dnuke-art/digital-pinhole/mockups/out/curved_grating_sheet.png

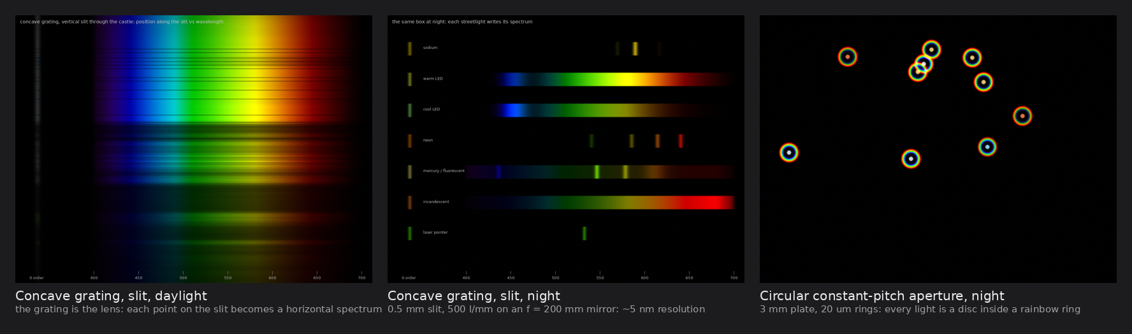
mockups/out/curved_grating_sheet.png
