dnuke-art/digital-pinhole/mockups/out/diag_01_relay.png

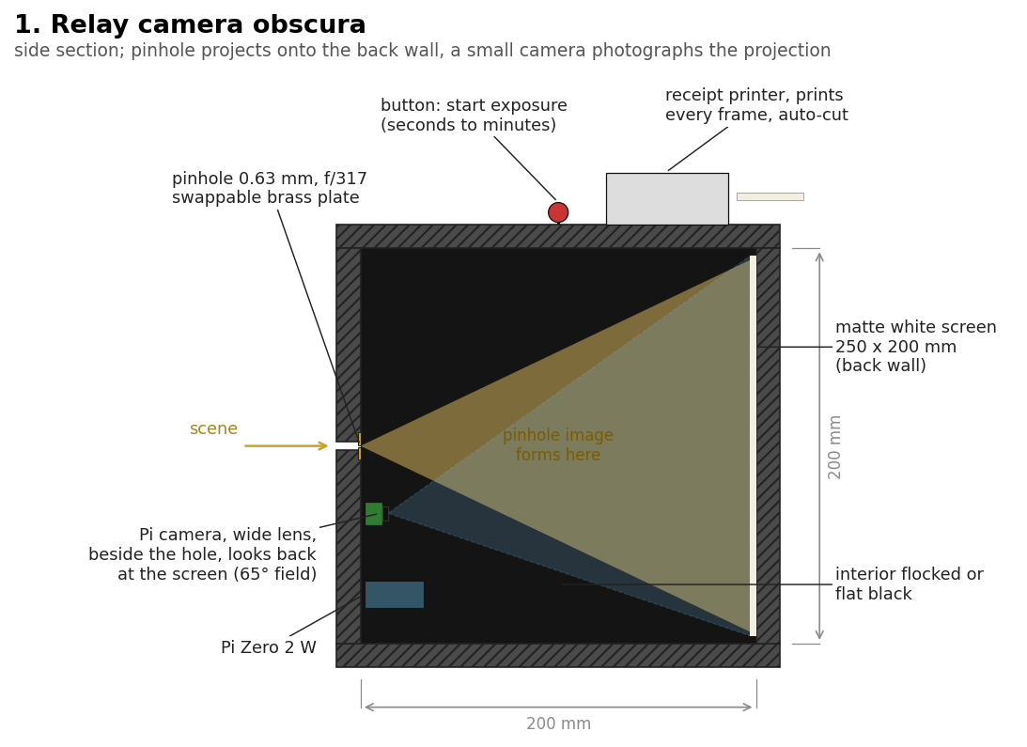
mockups/out/diag_01_relay.png
