dnuke-art/digital-pinhole/mockups/out/diag_02_wetplate.png

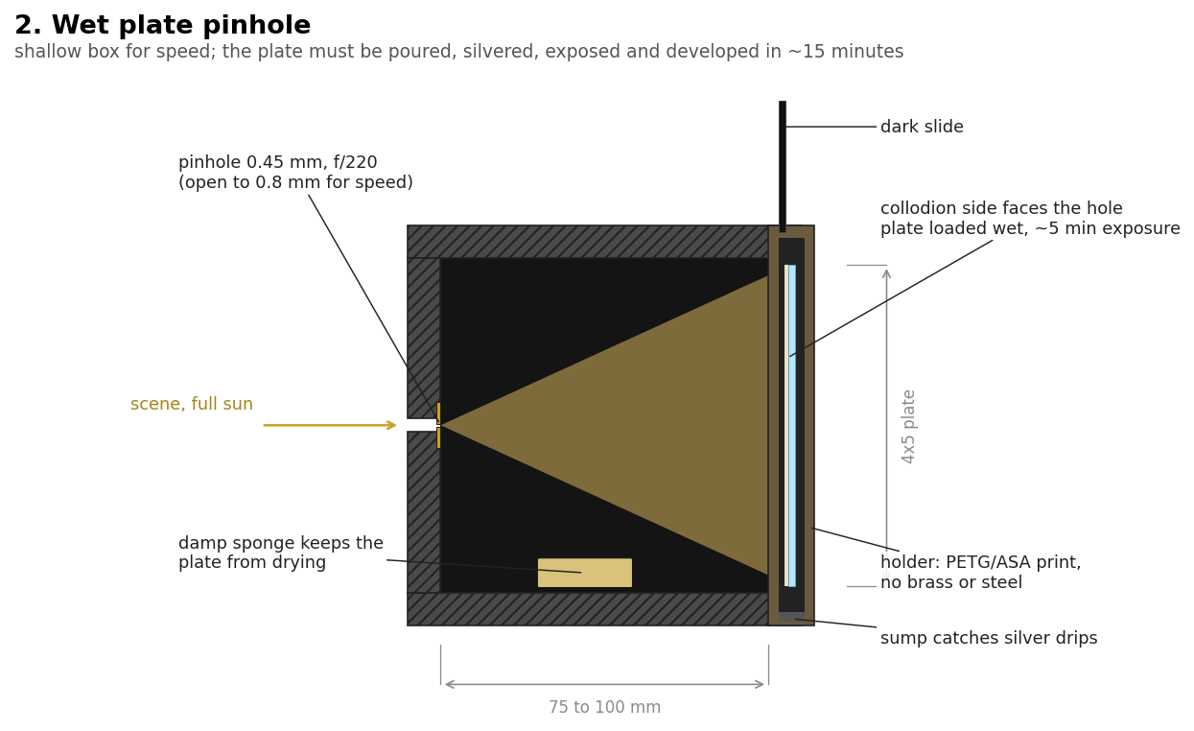
mockups/out/diag_02_wetplate.png
