dnuke-art/digital-pinhole/mockups/out/diag_03_swappable.png

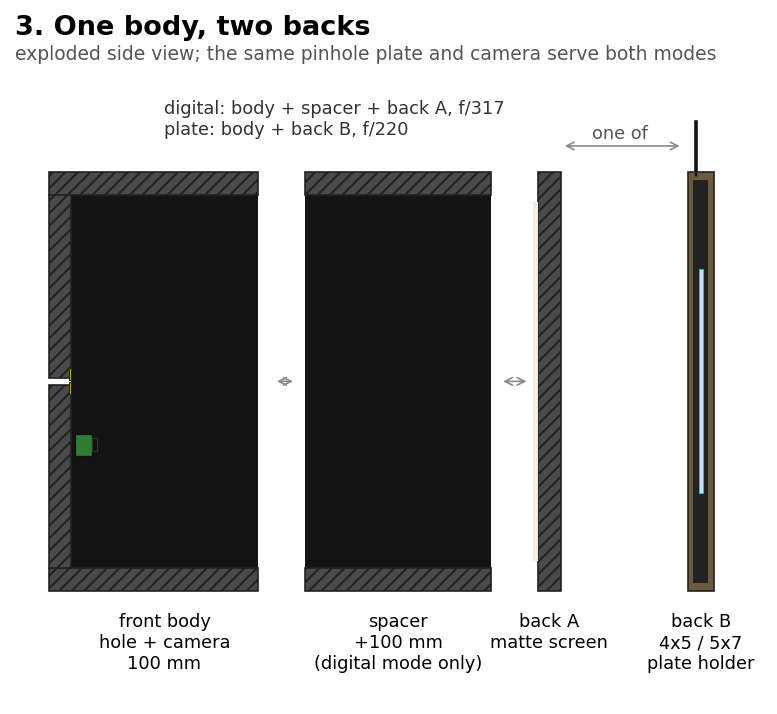
mockups/out/diag_03_swappable.png
