dnuke-art/digital-pinhole/mockups/out/diag_04_pihq.png

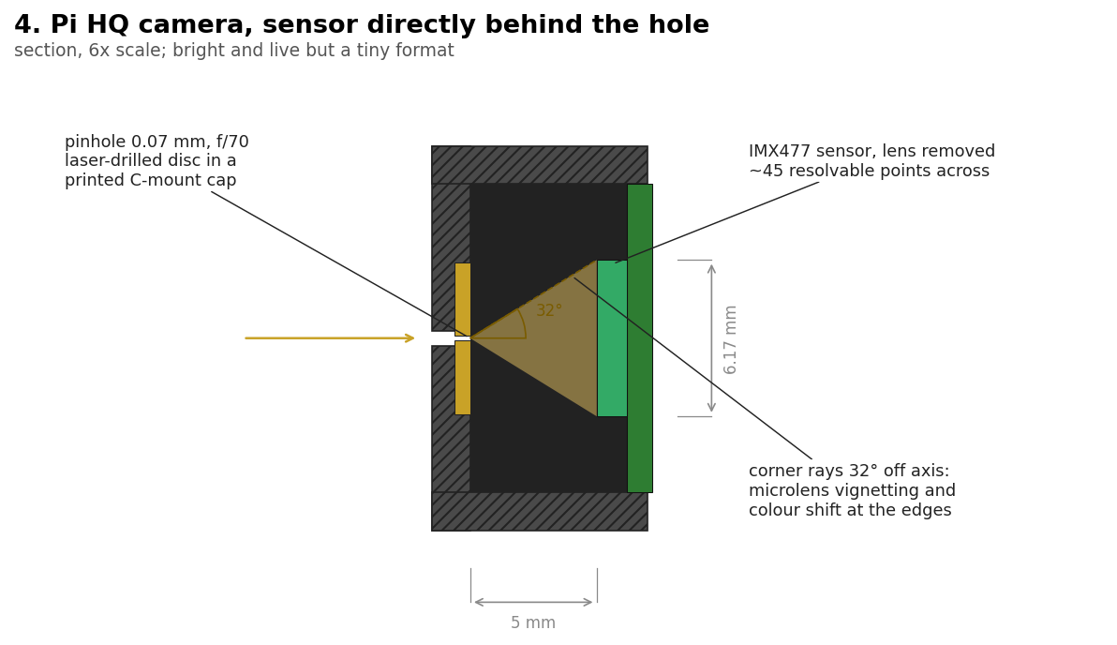
mockups/out/diag_04_pihq.png
