dnuke-art/digital-pinhole/mockups/out/diag_05_bodycap.png

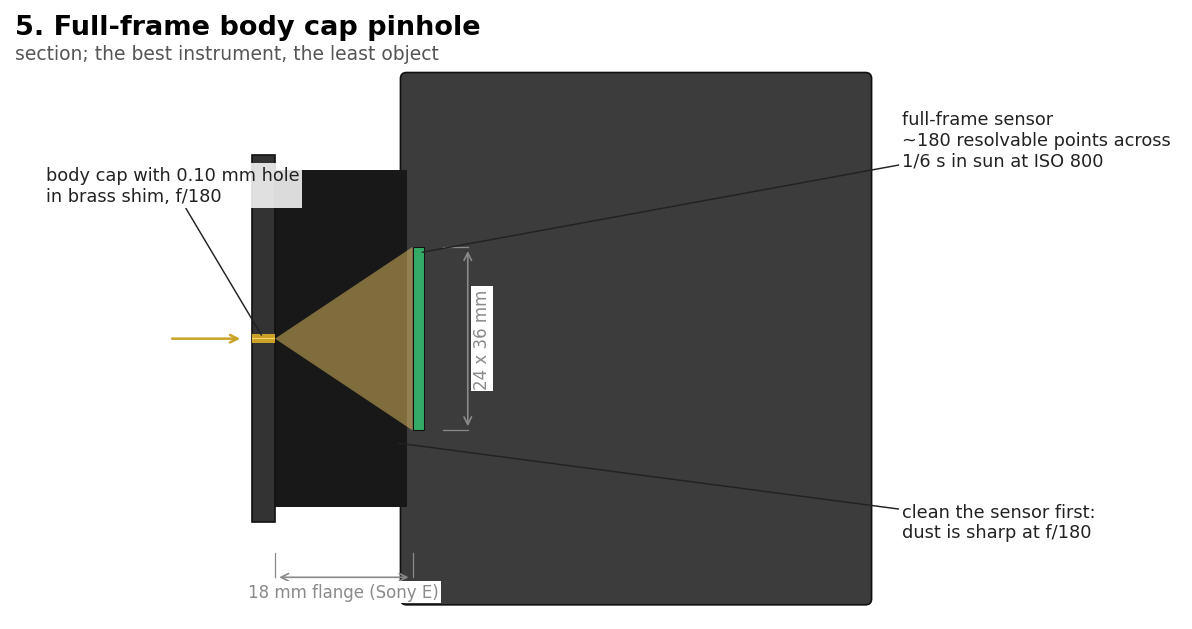
mockups/out/diag_05_bodycap.png
