dnuke-art/digital-pinhole/mockups/out/diag_06_suntrace.png

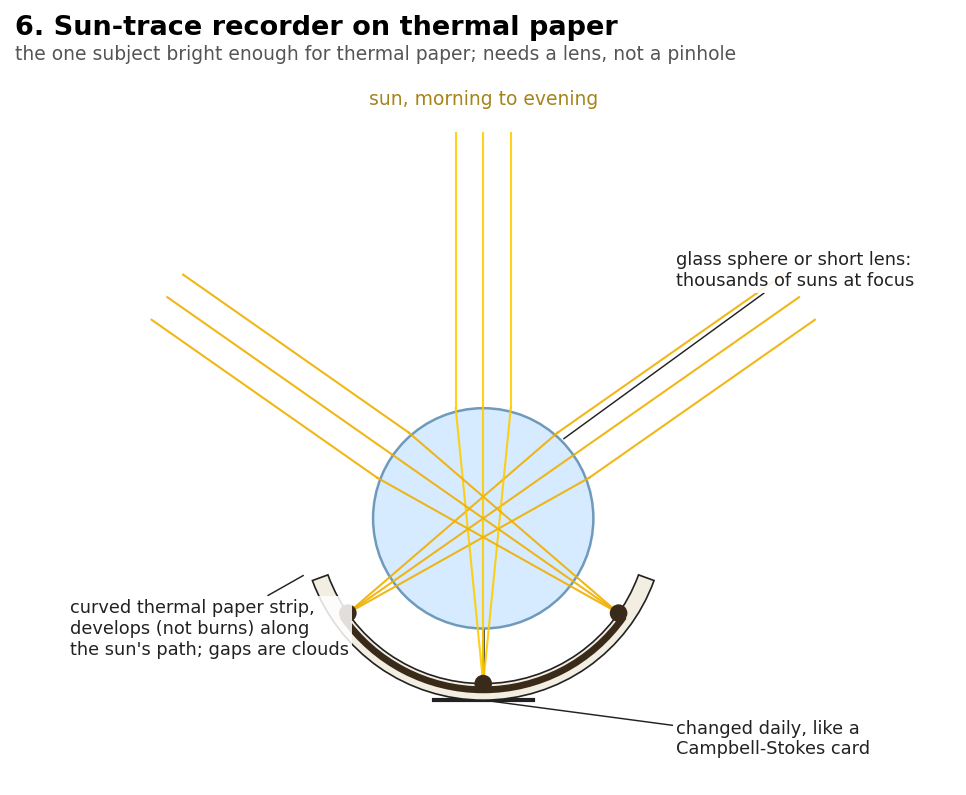
mockups/out/diag_06_suntrace.png
