dnuke-art/digital-pinhole/mockups/out/diag_07_dubroni.png

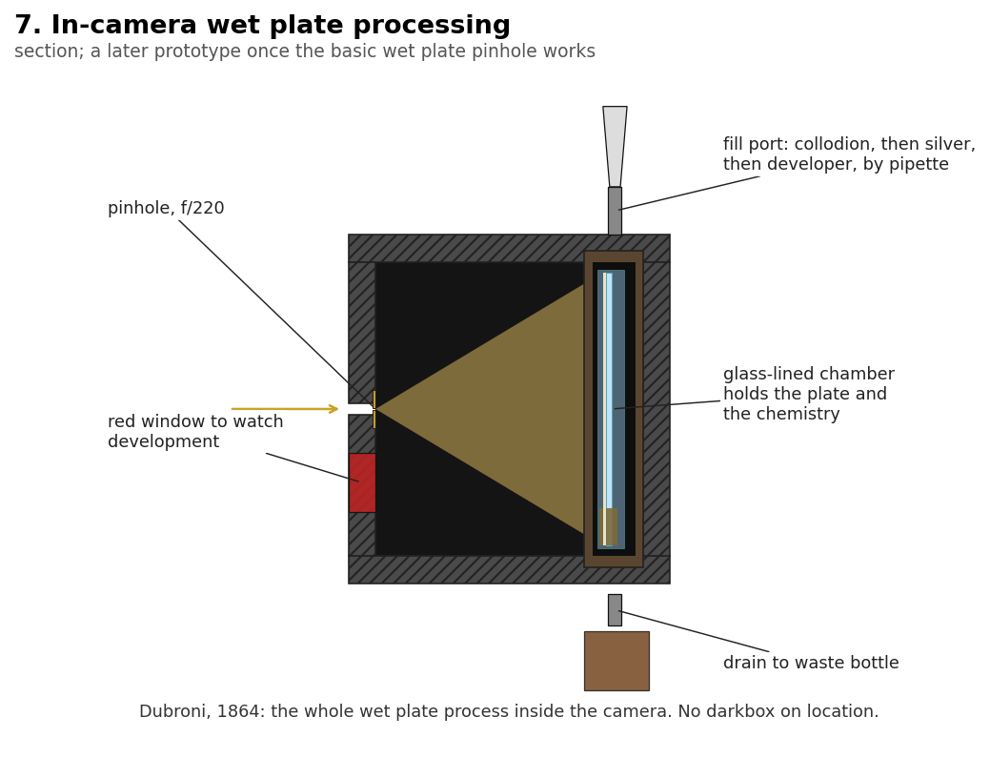
mockups/out/diag_07_dubroni.png
