dnuke-art/digital-pinhole/mockups/out/diag_08_show.png

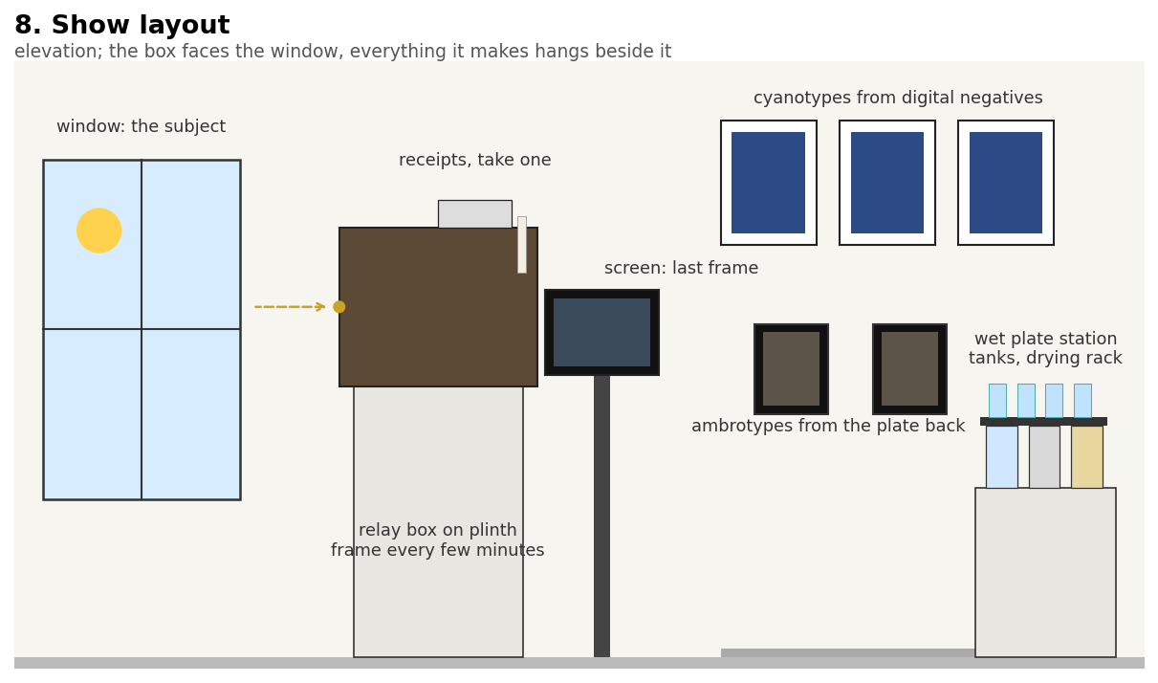
mockups/out/diag_08_show.png
