dnuke-art/digital-pinhole/mockups/out/diag_09_rowland.png

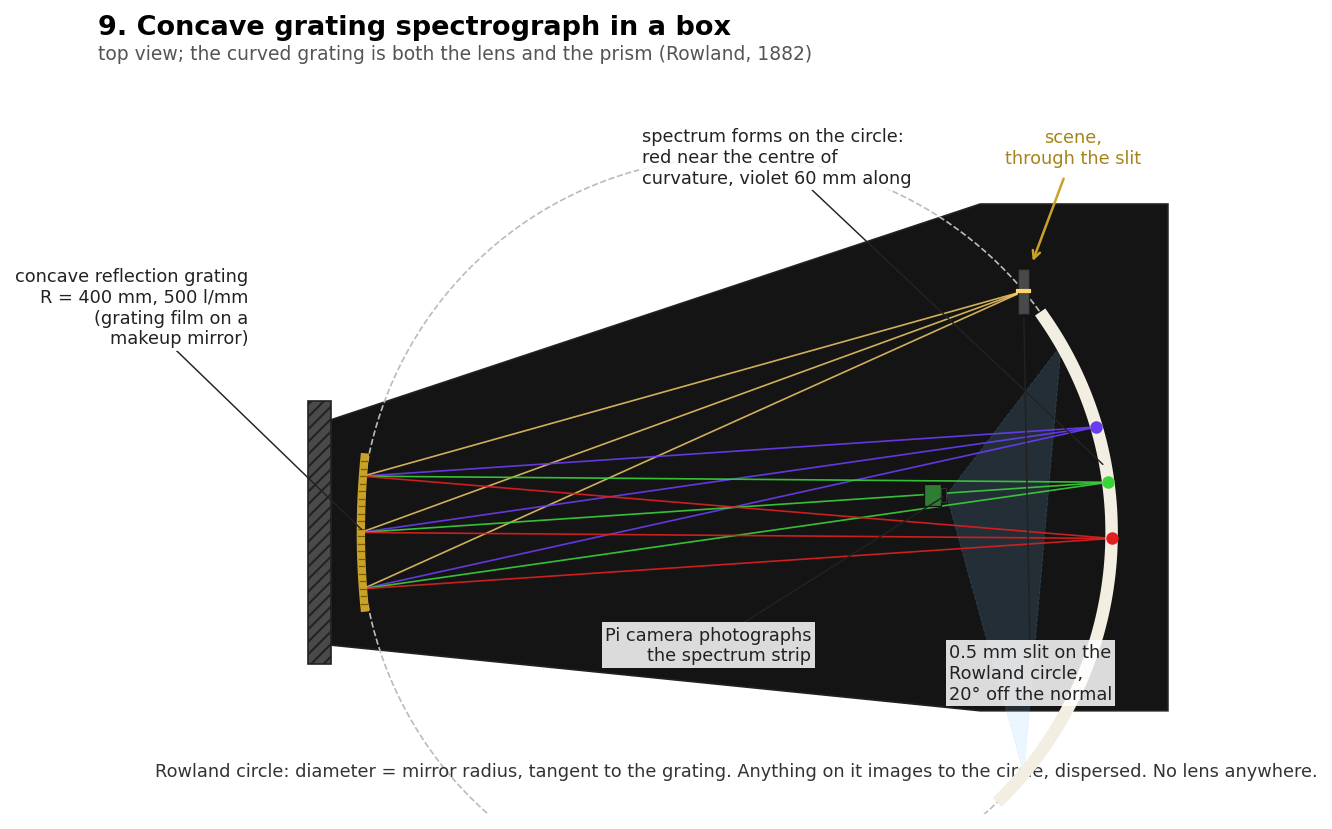
mockups/out/diag_09_rowland.png
