dnuke-art/digital-pinhole/mockups/out/diagrams_sheet.png

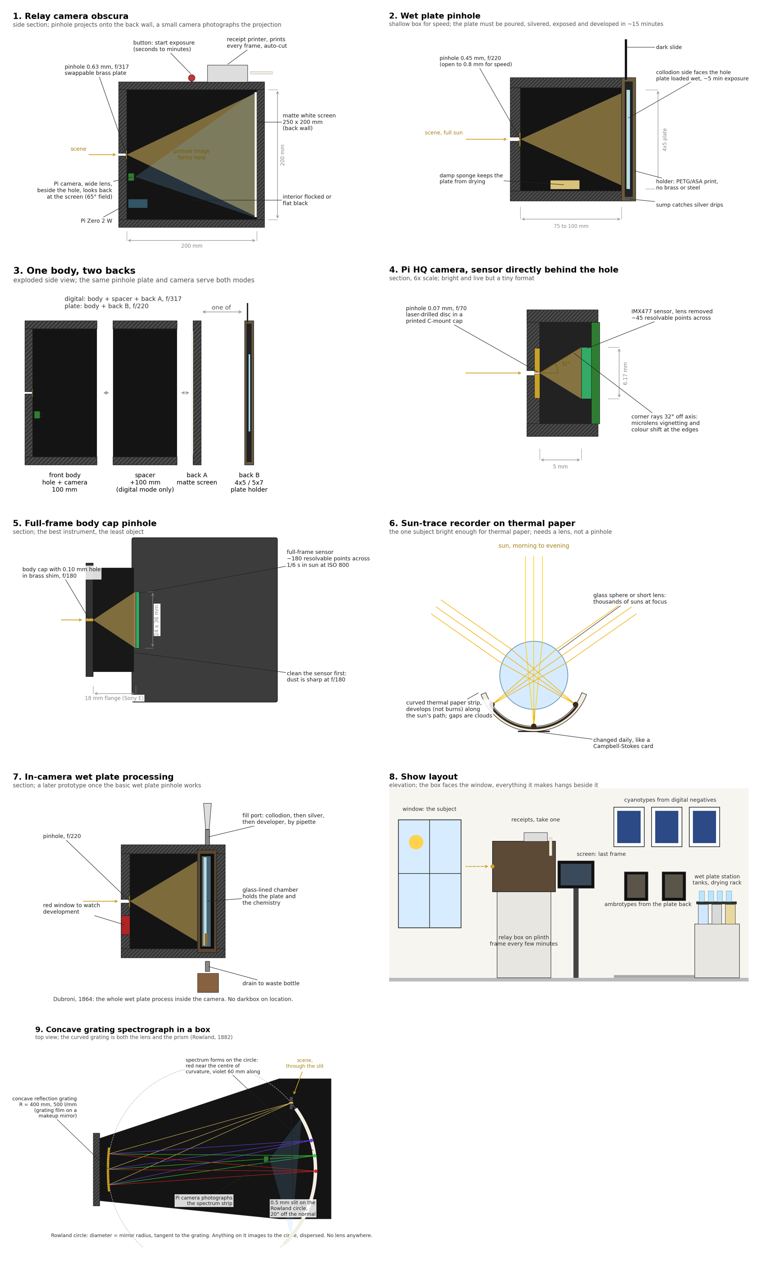
mockups/out/diagrams_sheet.png
