dnuke-art/digital-pinhole/mockups/out/dither_01_floyd.png

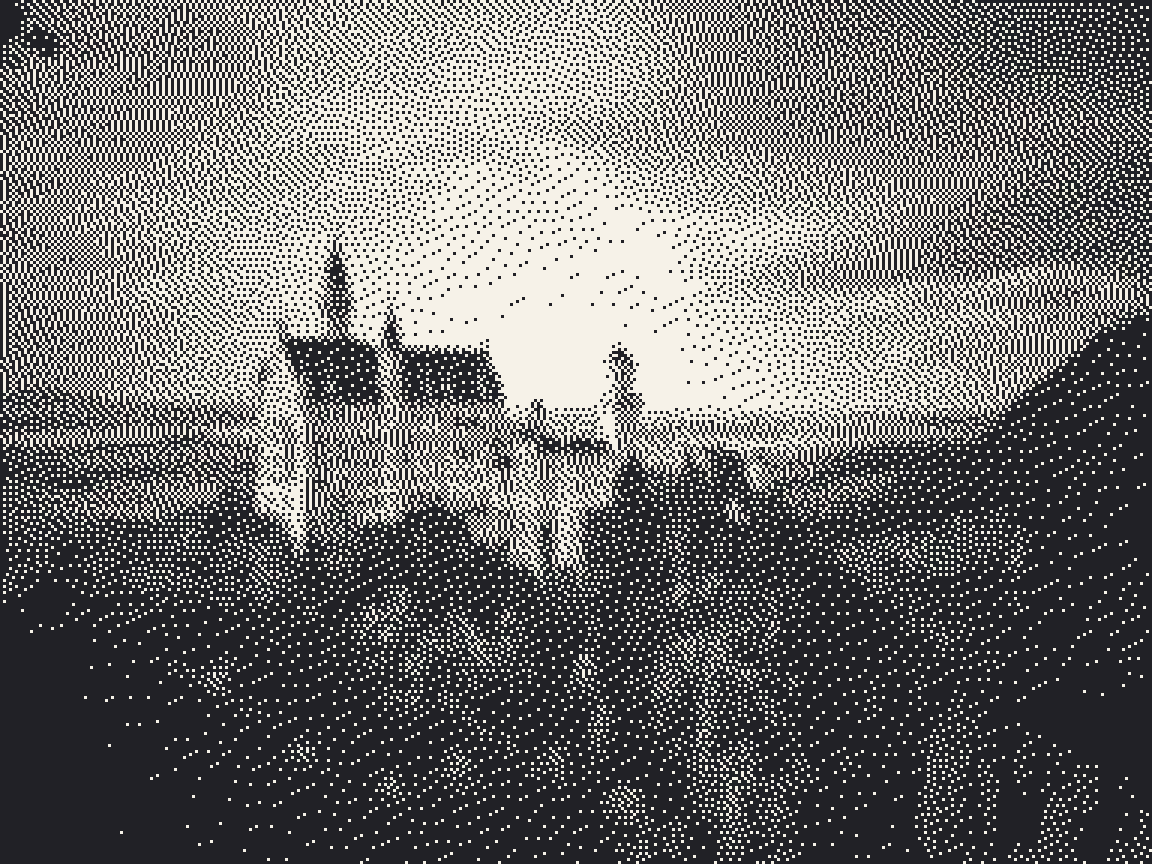
mockups/out/dither_01_floyd.png
