dnuke-art/digital-pinhole/mockups/out/dither_05_halftone.png

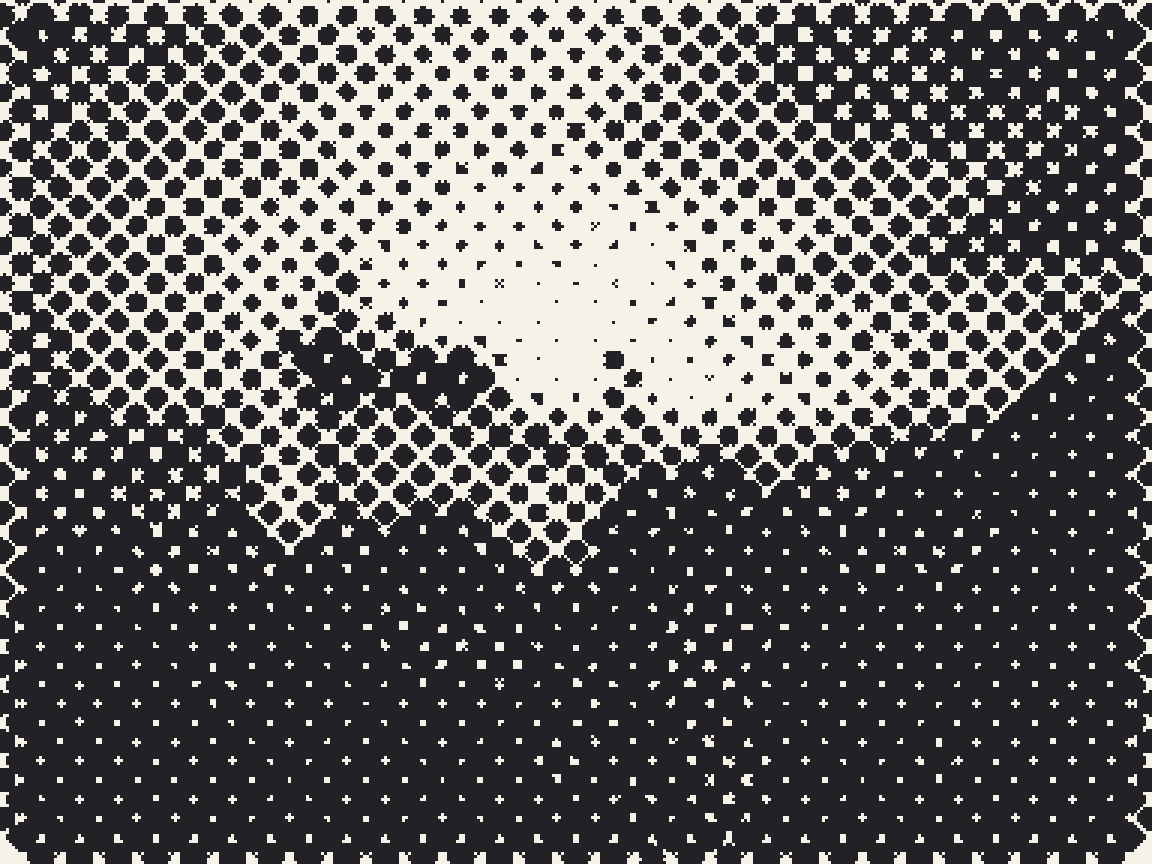
mockups/out/dither_05_halftone.png
