dnuke-art/digital-pinhole/mockups/out/dither_06_linescreen.png

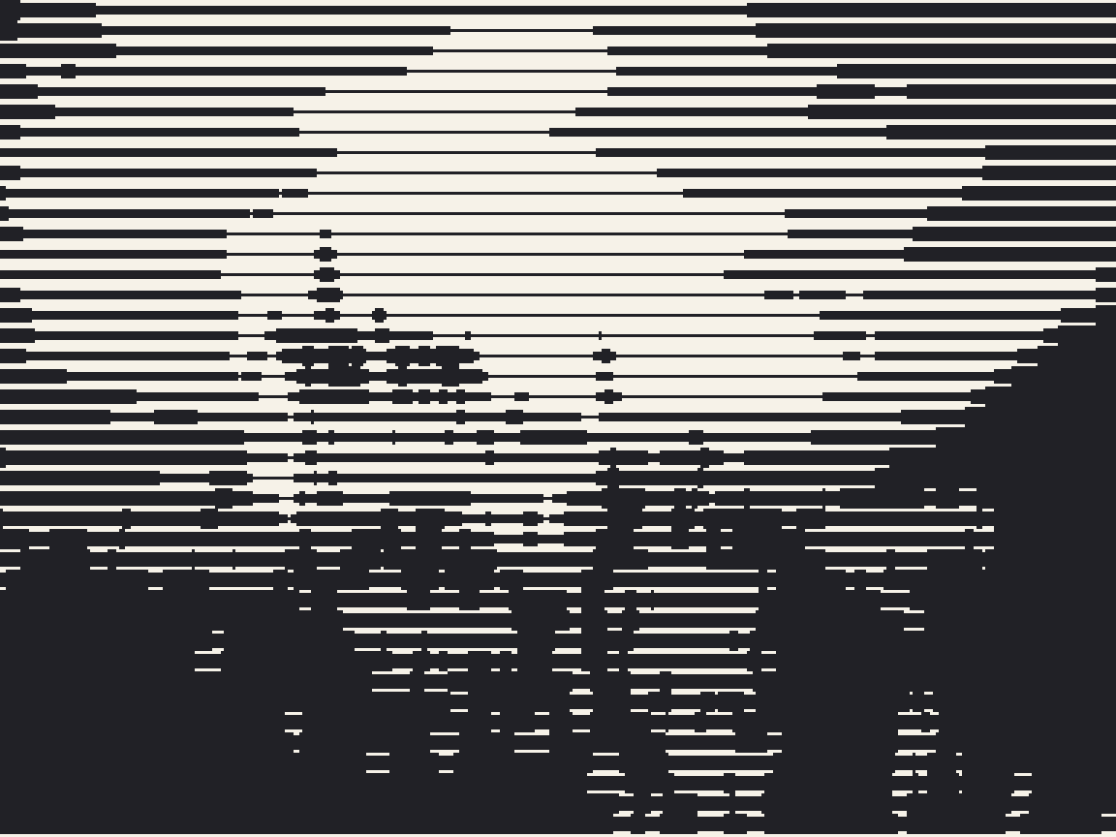
mockups/out/dither_06_linescreen.png
