dnuke-art/digital-pinhole/mockups/out/dither_08_cga.png

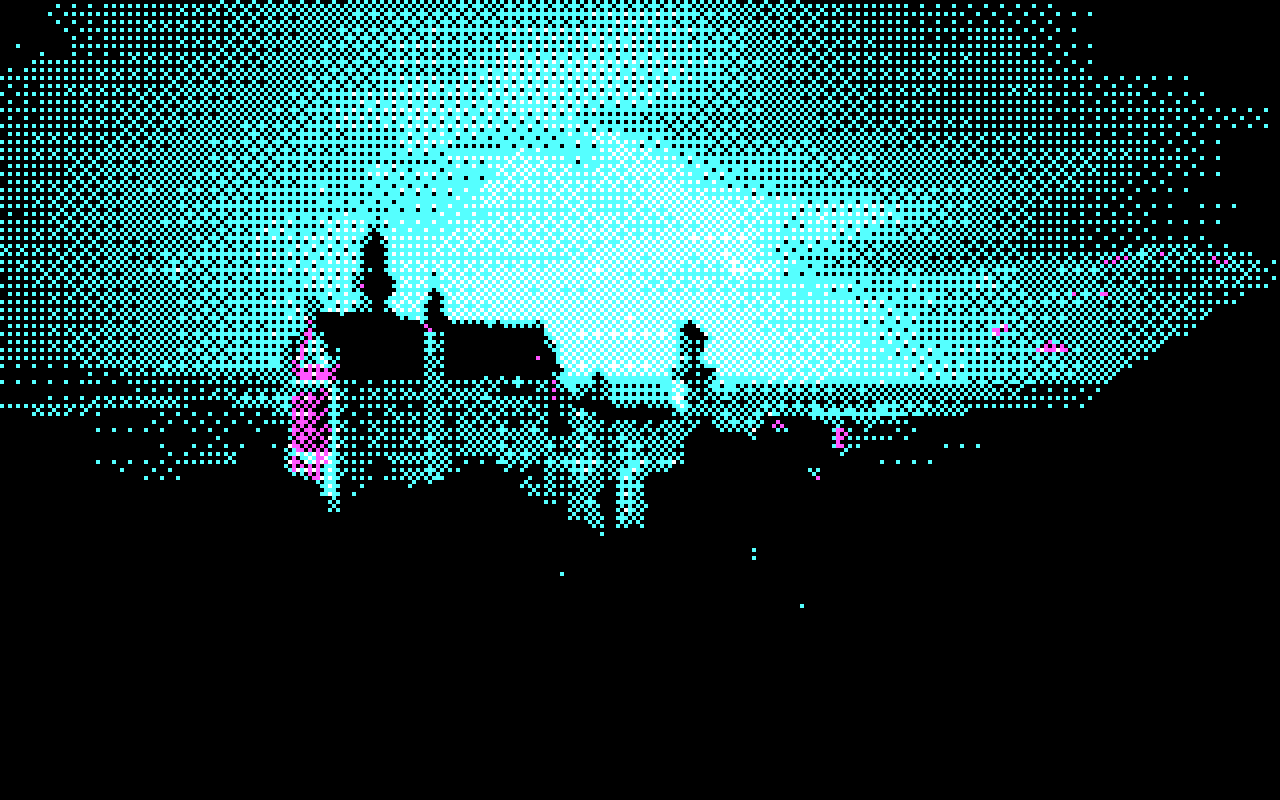
mockups/out/dither_08_cga.png
