dnuke-art/digital-pinhole/mockups/out/dither_09_chunky.png

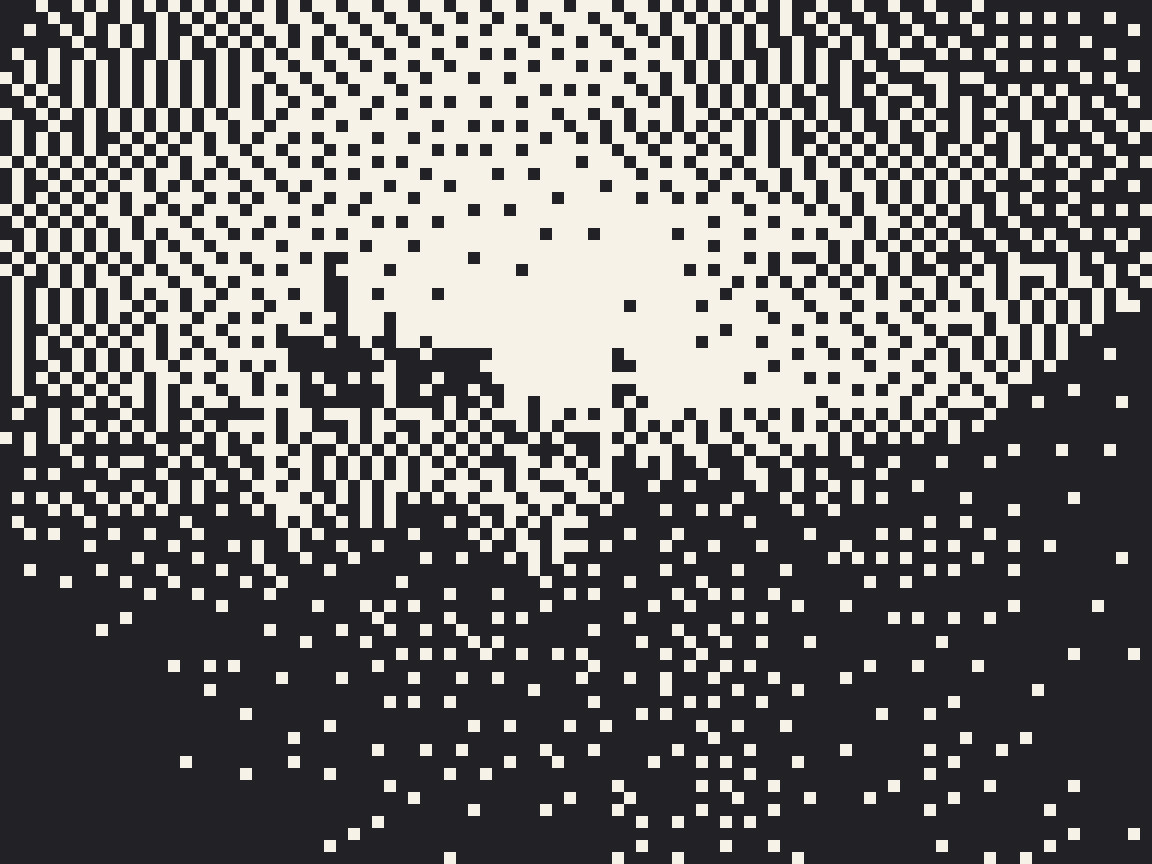
mockups/out/dither_09_chunky.png
