dnuke-art/digital-pinhole/mockups/out/dither_sheet.png

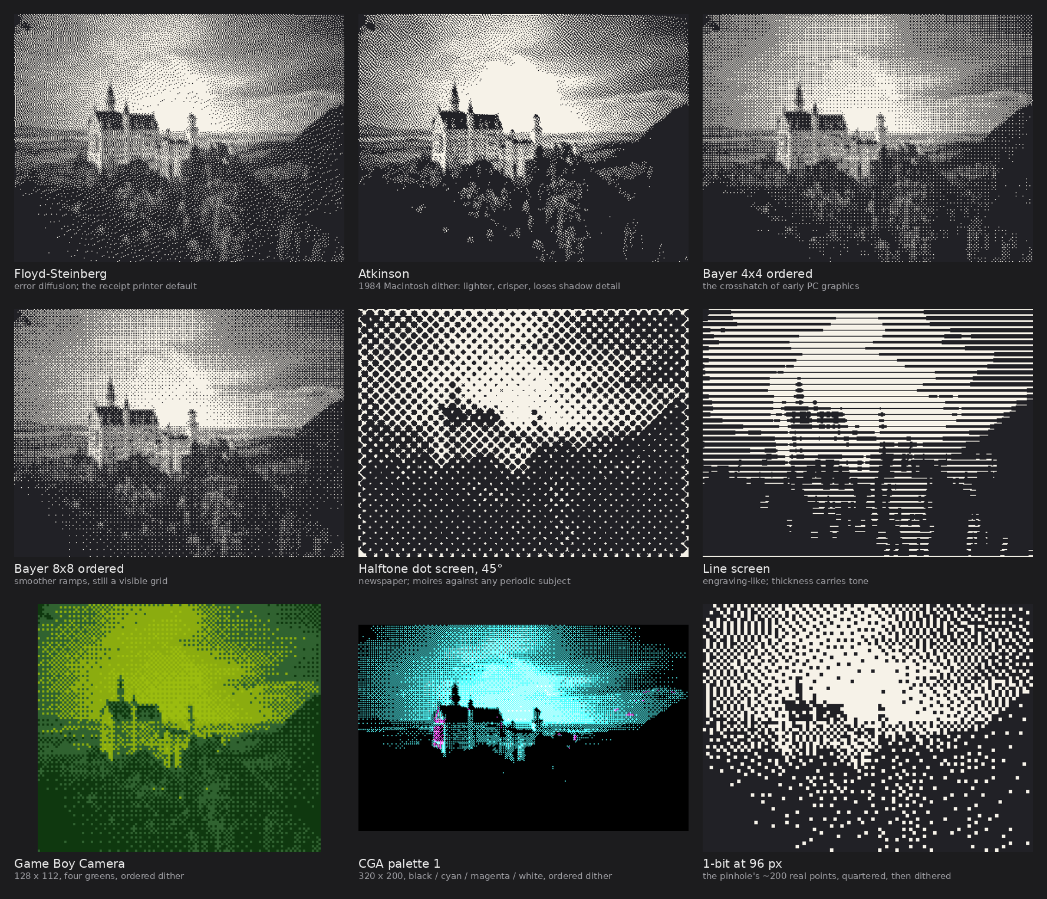
mockups/out/dither_sheet.png
