dnuke-art/digital-pinhole/mockups/out/grating_sheet.png

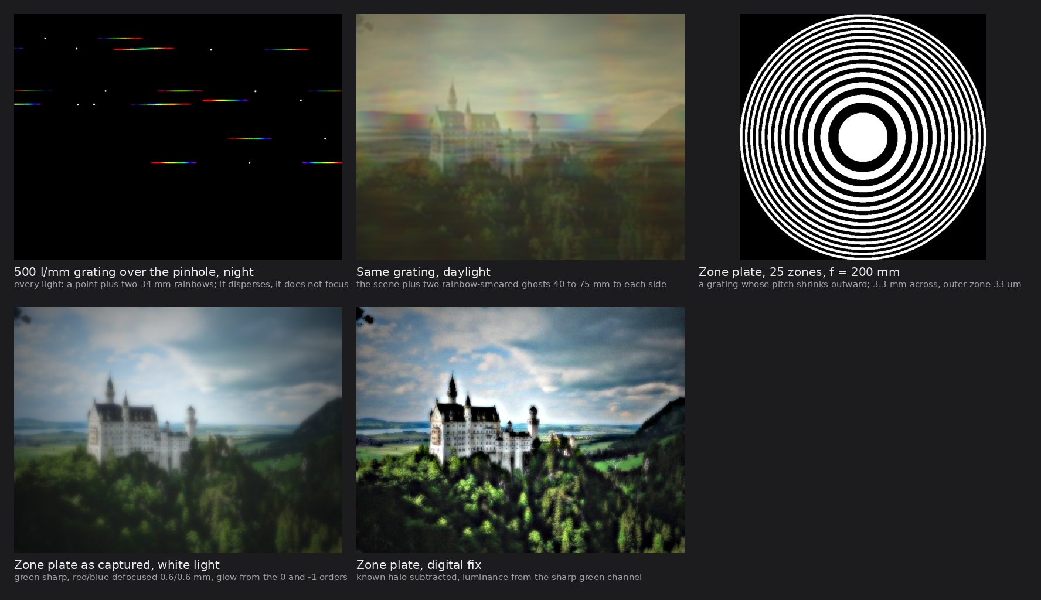
mockups/out/grating_sheet.png
