dnuke-art/digital-pinhole/mockups/out/look2_03_double_slit_fringes.png

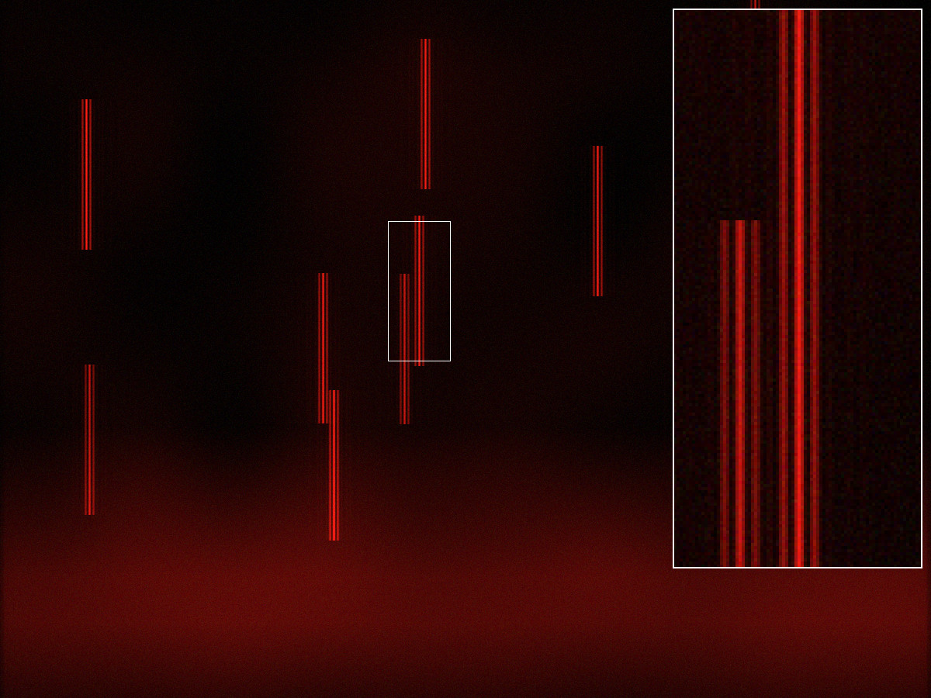
mockups/out/look2_03_double_slit_fringes.png
