dnuke-art/digital-pinhole/mockups/out/look2_06_moire.png

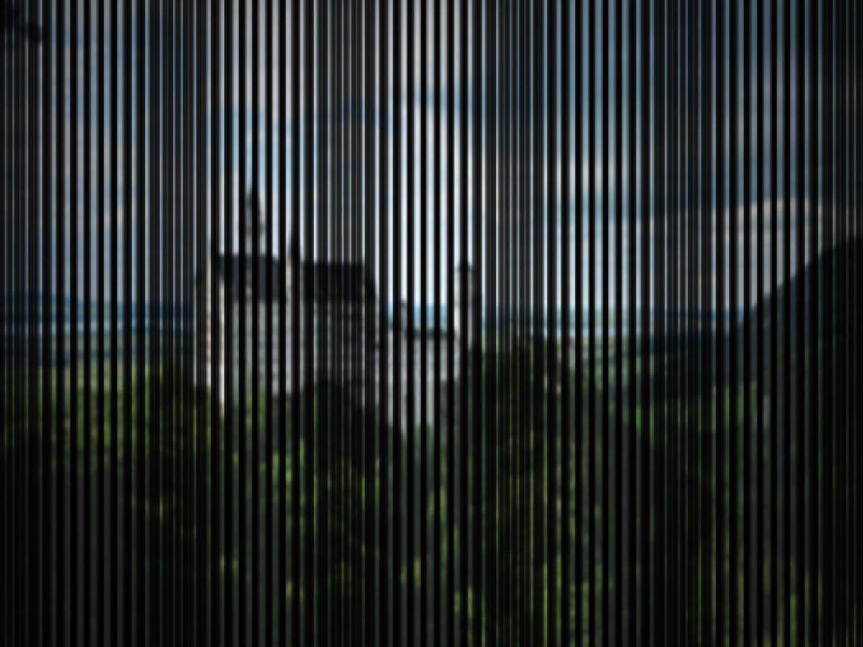
mockups/out/look2_06_moire.png
