dnuke-art/digital-pinhole/mockups/out/look2_07_star_pinhole.png

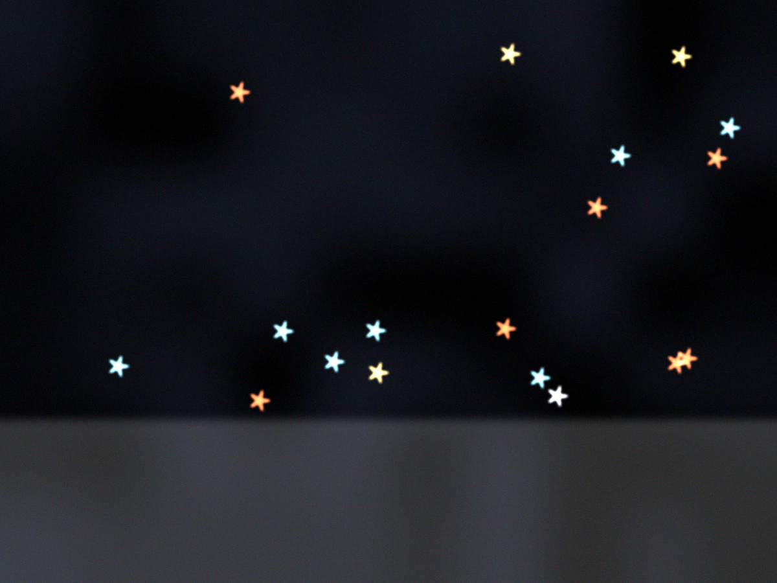
mockups/out/look2_07_star_pinhole.png
