dnuke-art/digital-pinhole/mockups/out/look2_09_mura_mask.png

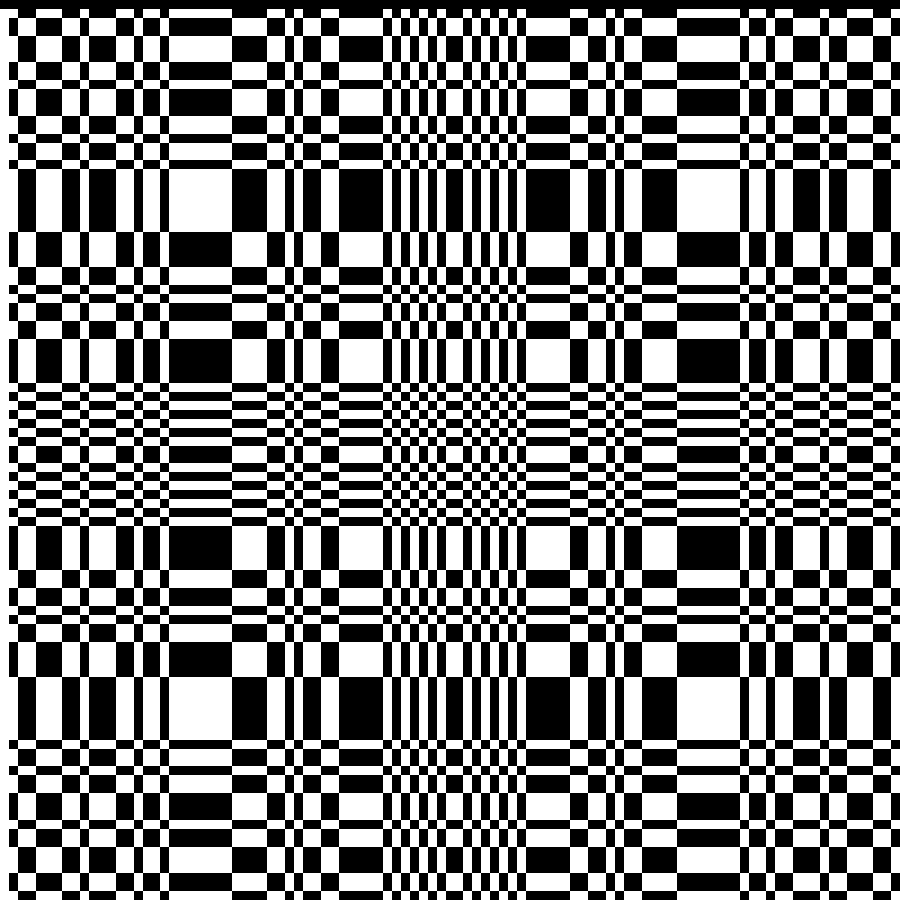
mockups/out/look2_09_mura_mask.png
