dnuke-art/digital-pinhole/mockups/out/look2_10_mura_raw.png

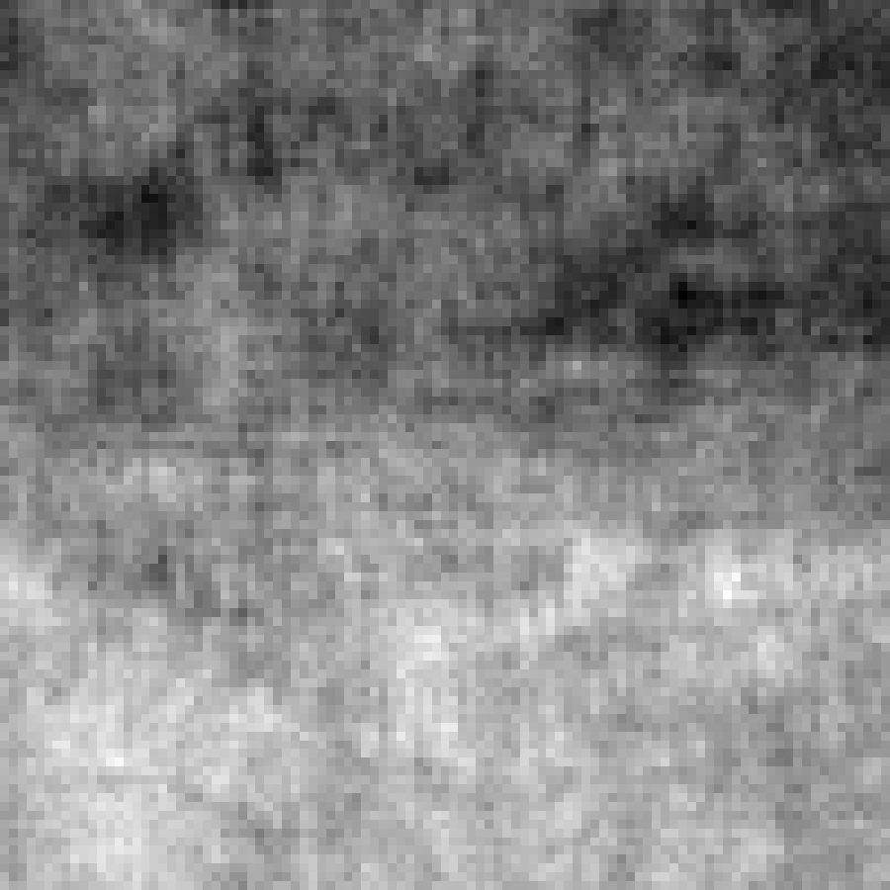
mockups/out/look2_10_mura_raw.png
