dnuke-art/digital-pinhole/mockups/out/look2_11_mura_decoded.png

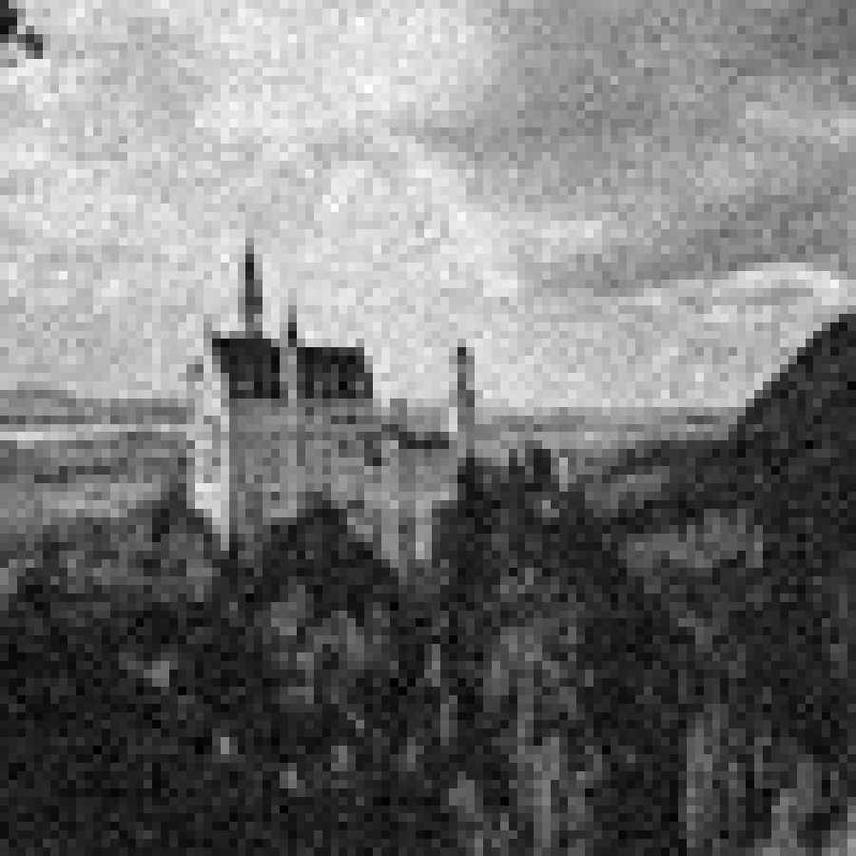
mockups/out/look2_11_mura_decoded.png
