dnuke-art/digital-pinhole/mockups/out/look2_13_slit_scan.png

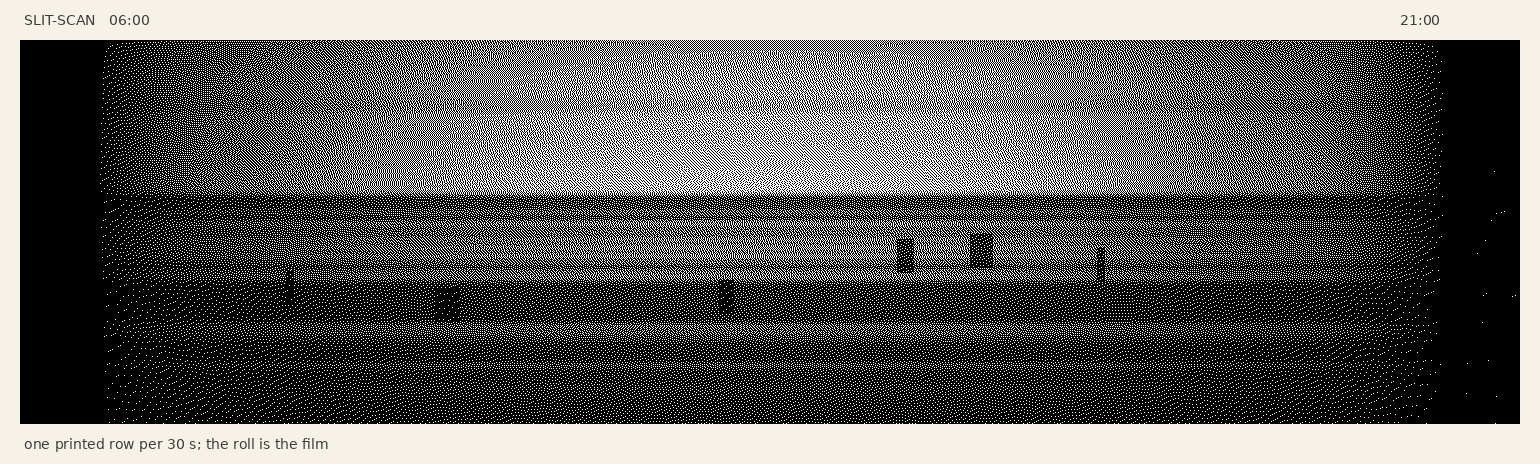
mockups/out/look2_13_slit_scan.png
