dnuke-art/digital-pinhole/mockups/out/look3_01_grating_night.png

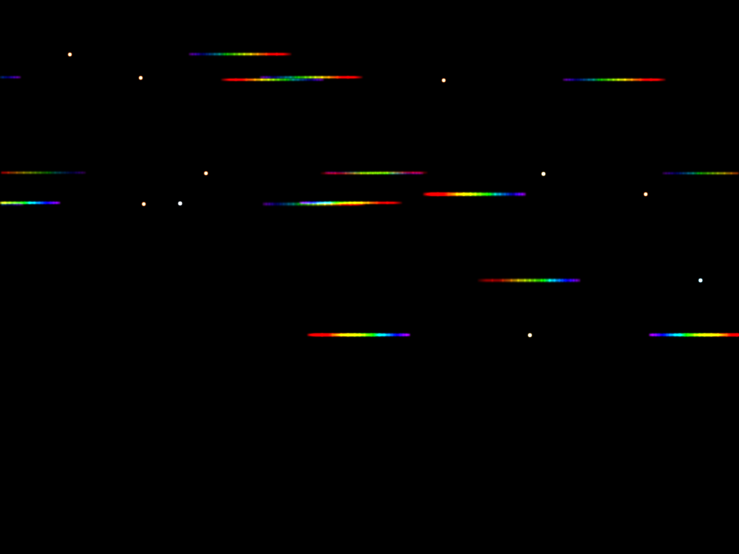
mockups/out/look3_01_grating_night.png
