dnuke-art/digital-pinhole/mockups/out/look3_02_grating_day.png

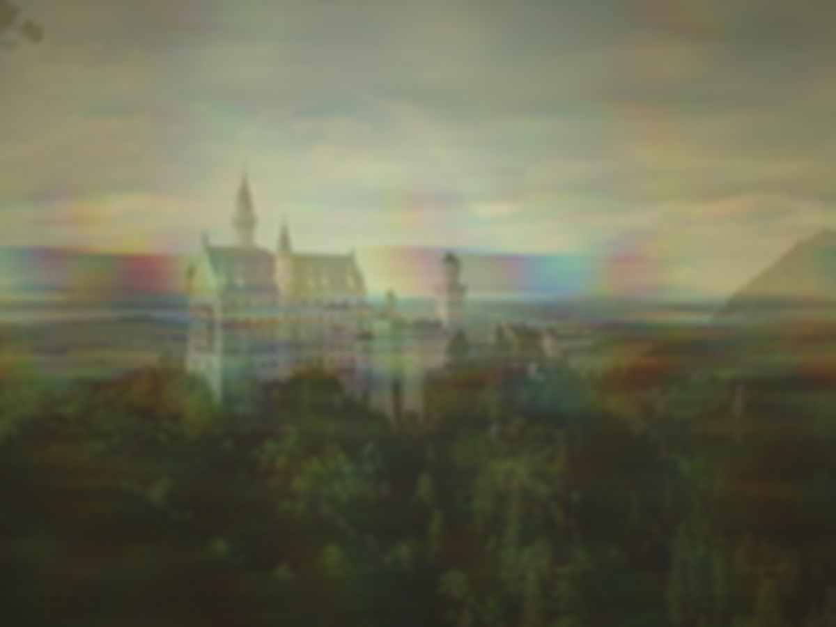
mockups/out/look3_02_grating_day.png
