dnuke-art/digital-pinhole/mockups/out/look3_03_zone_plate_pattern.png

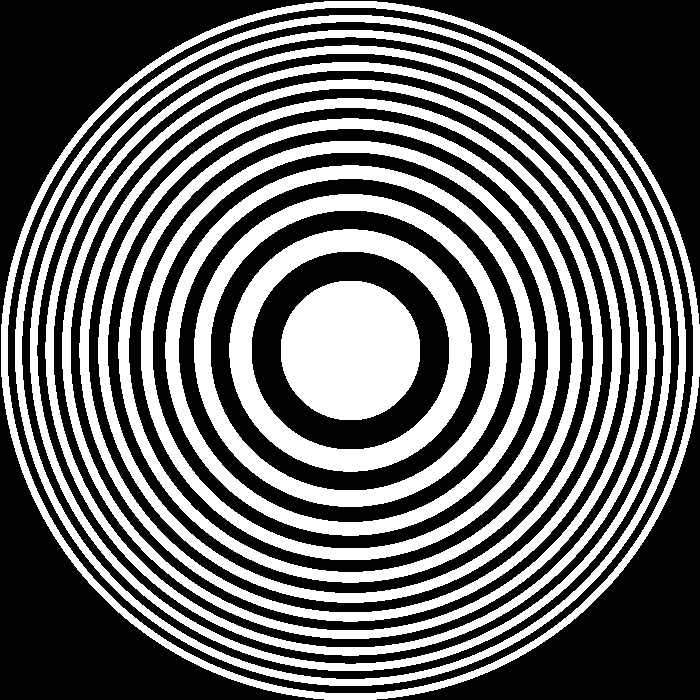
mockups/out/look3_03_zone_plate_pattern.png
