dnuke-art/digital-pinhole/mockups/out/look_02_fullframe_bodycap.png

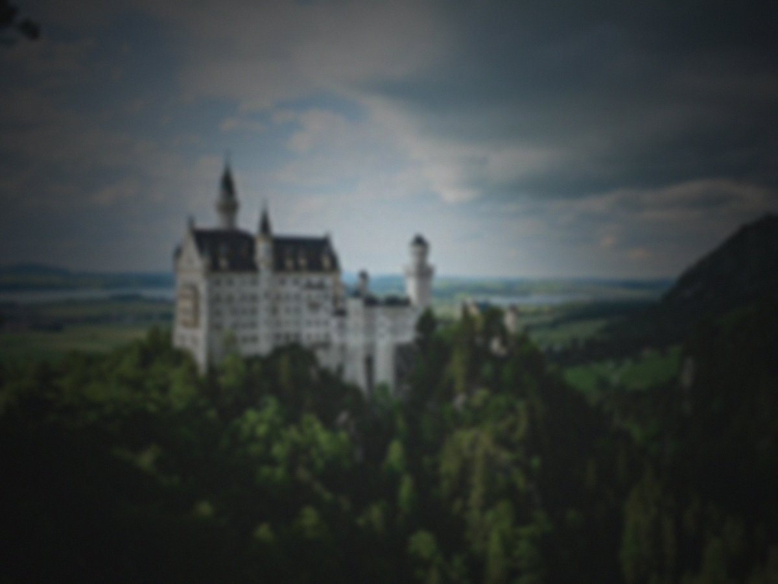
mockups/out/look_02_fullframe_bodycap.png
