dnuke-art/digital-pinhole/mockups/out/look_04_receipt.png

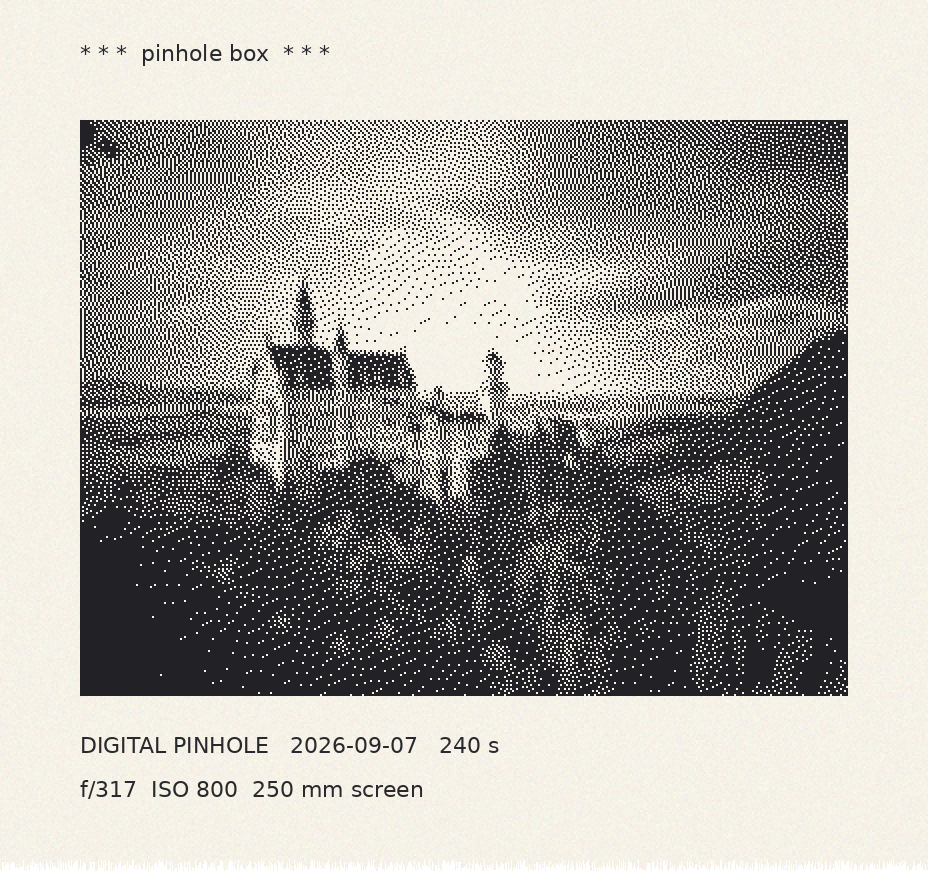
mockups/out/look_04_receipt.png
