dnuke-art/digital-pinhole/mockups/out/look_05_cyanotype.png

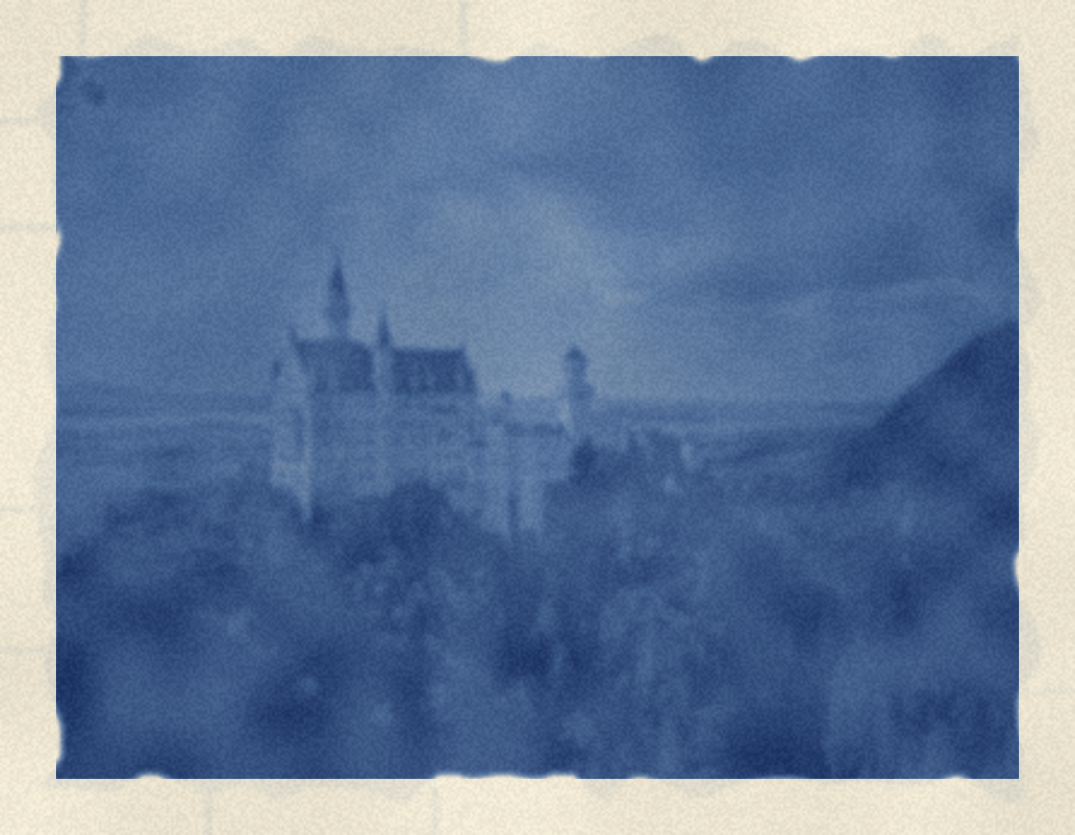
mockups/out/look_05_cyanotype.png
