dnuke-art/digital-pinhole/mockups/out/look_06_collodion_landscape.png

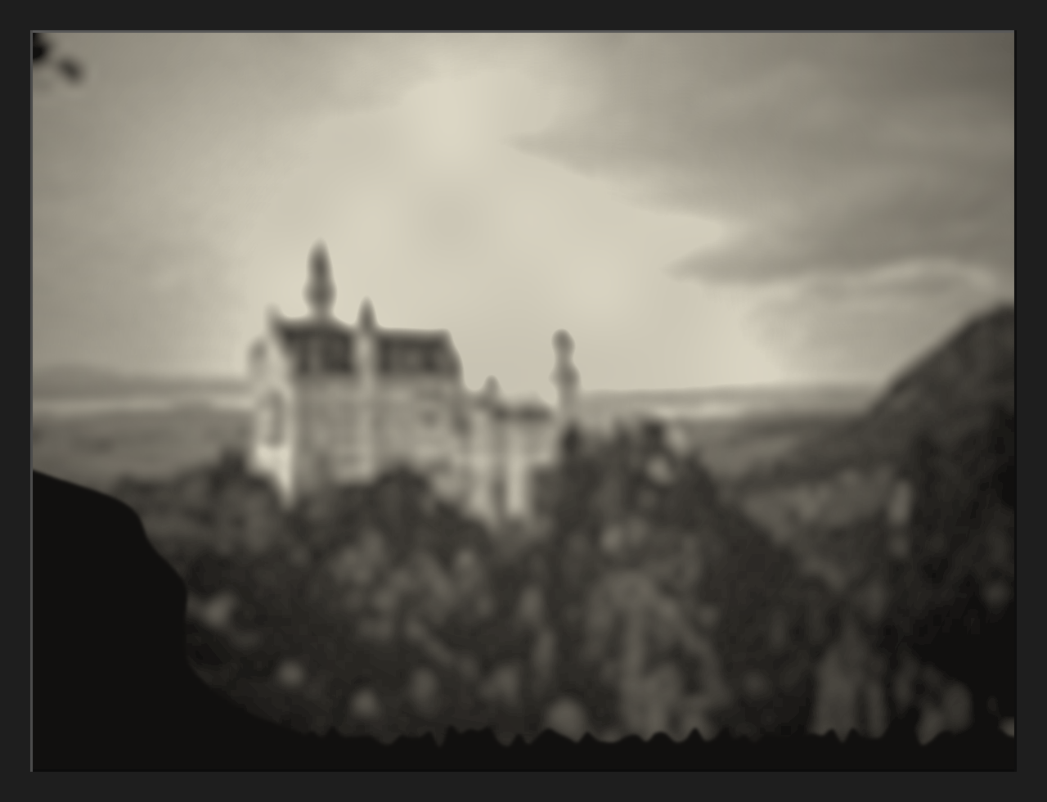
mockups/out/look_06_collodion_landscape.png
