dnuke-art/digital-pinhole/mockups/out/look_07_collodion_portrait.png

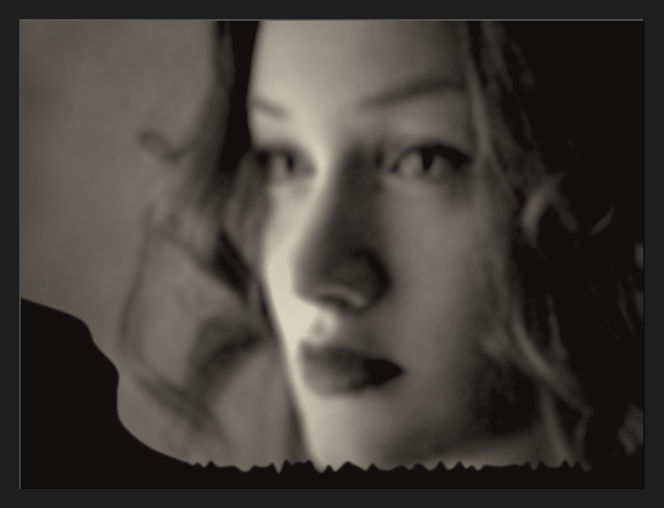
mockups/out/look_07_collodion_portrait.png
