dnuke-art/digital-pinhole/mockups/out/look_08_solargraph.png

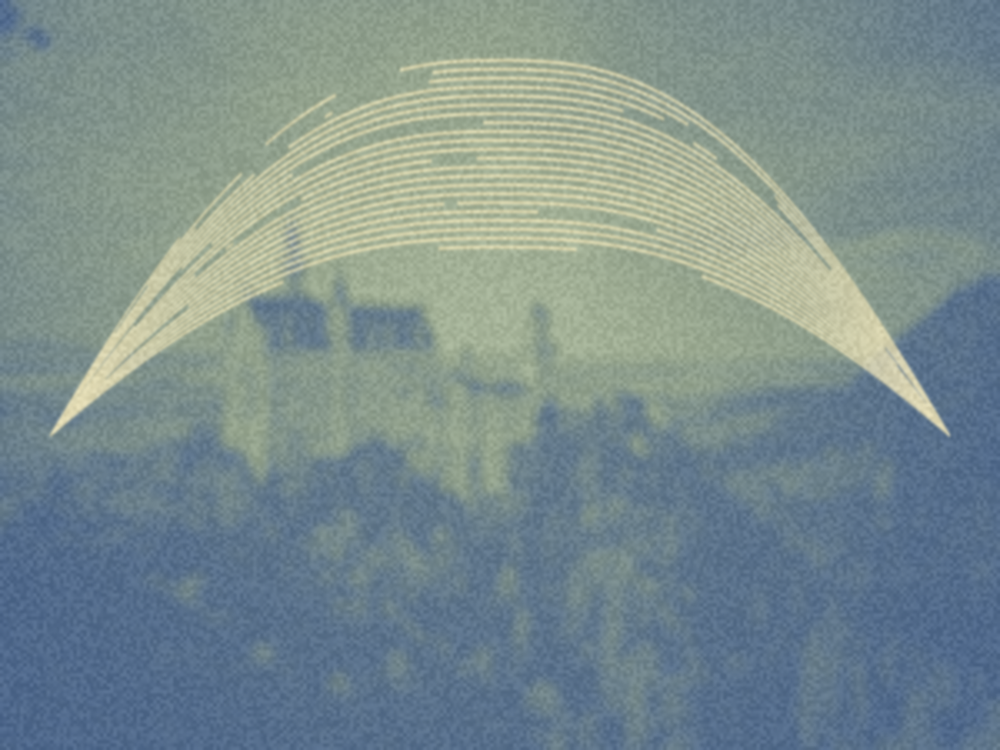
mockups/out/look_08_solargraph.png
