dnuke-art/digital-pinhole/mockups/out/look_09_sun_trace.png

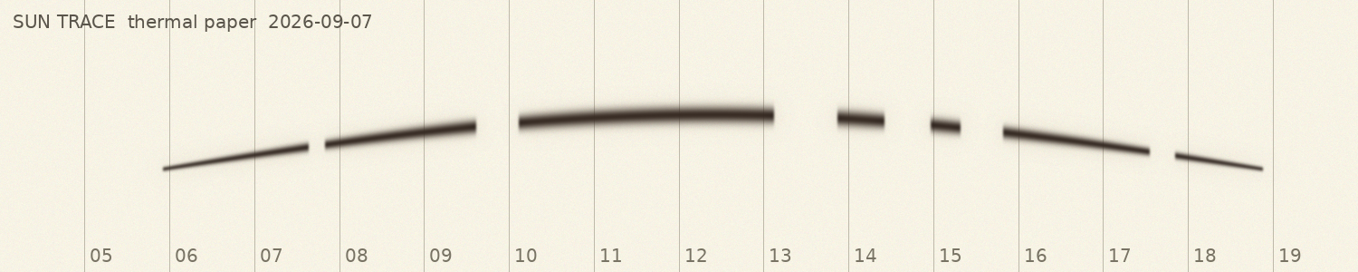
mockups/out/look_09_sun_trace.png
