dnuke-art/digital-pinhole/mockups/out/look_10_heliograph.png

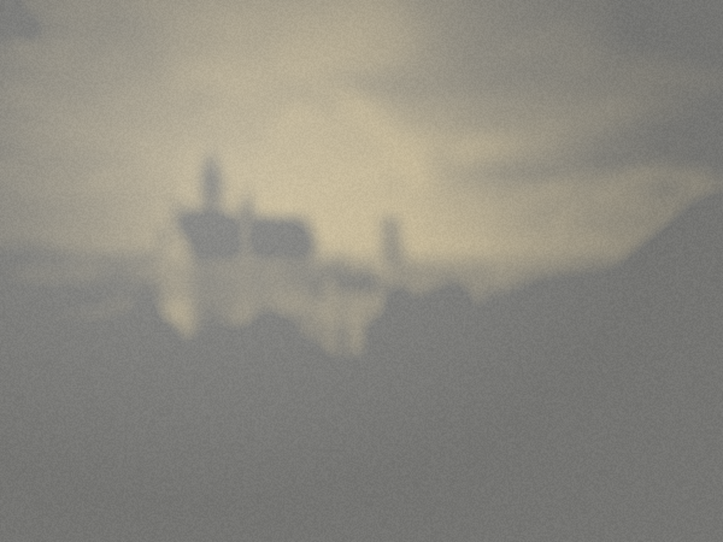
mockups/out/look_10_heliograph.png
