dnuke-art/digital-pinhole/mockups/out/looks_sheet.png

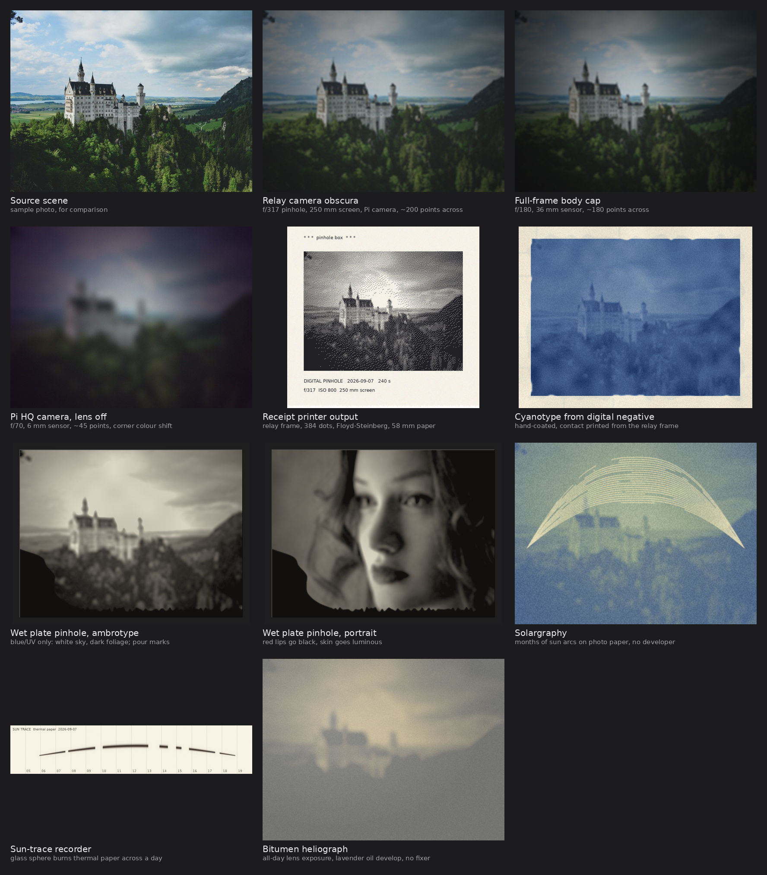
mockups/out/looks_sheet.png
