dnuke-art/digital-pinhole/mockups/out/render_relay_cutaway.png

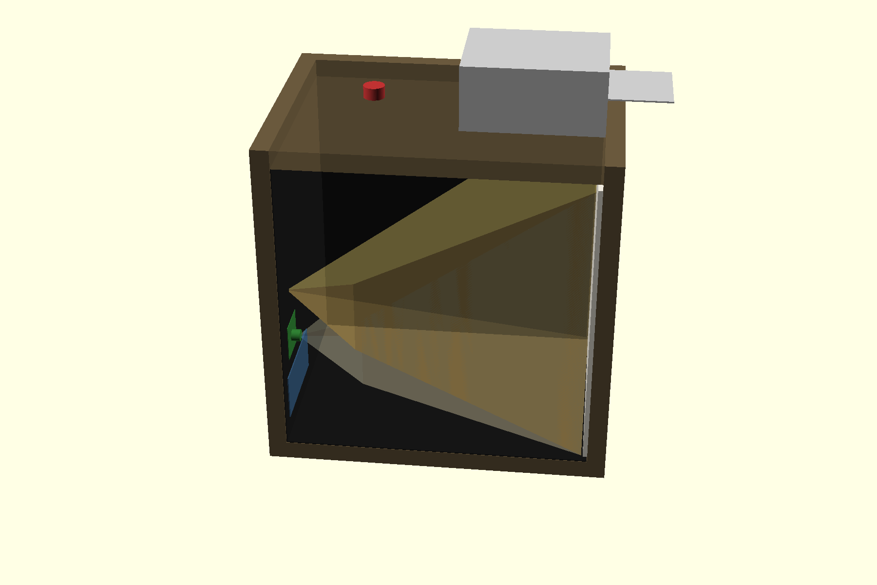
mockups/out/render_relay_cutaway.png
