dnuke-art/digital-pinhole/mockups/src/pic_1027.jpg

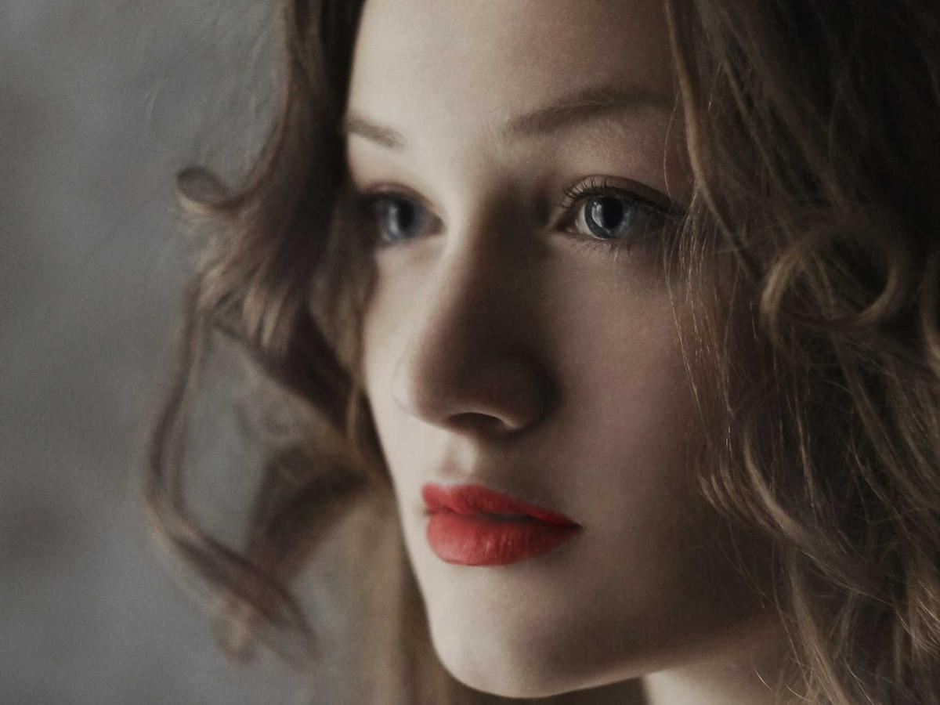
mockups/src/pic_1027.jpg
